oskar2517/crt-calculator/assets/2.jpg

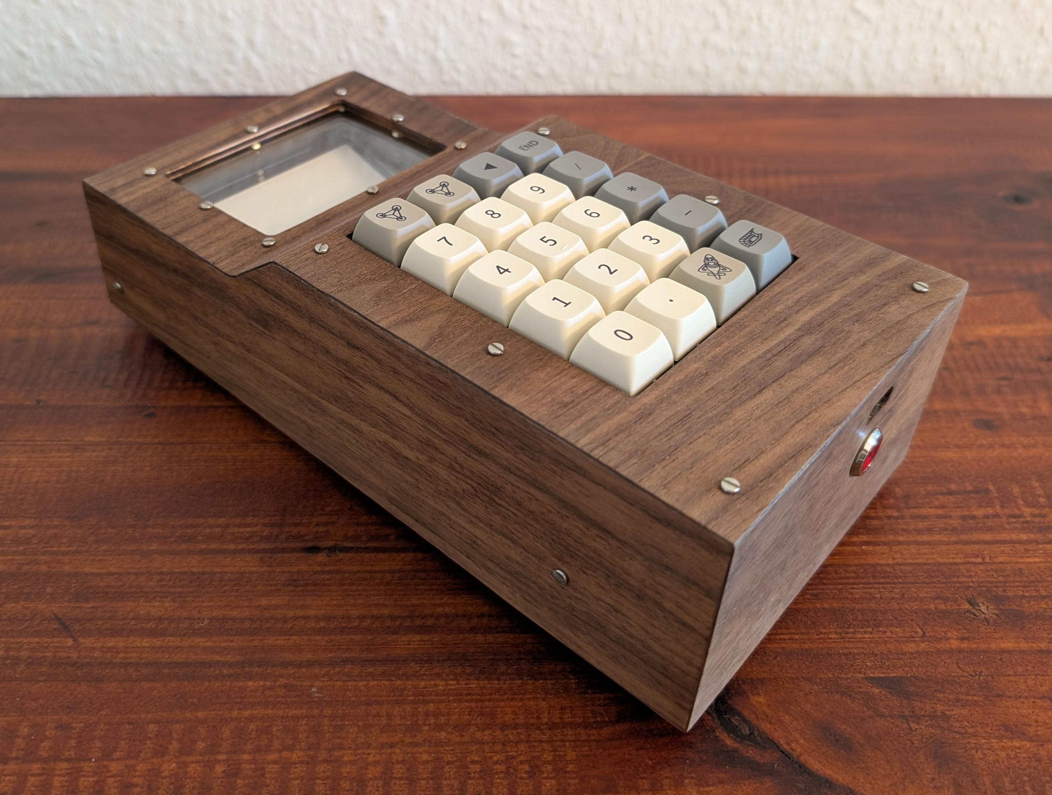
assets/2.jpg
