oskar2517/crt-calculator/assets/9.JPG

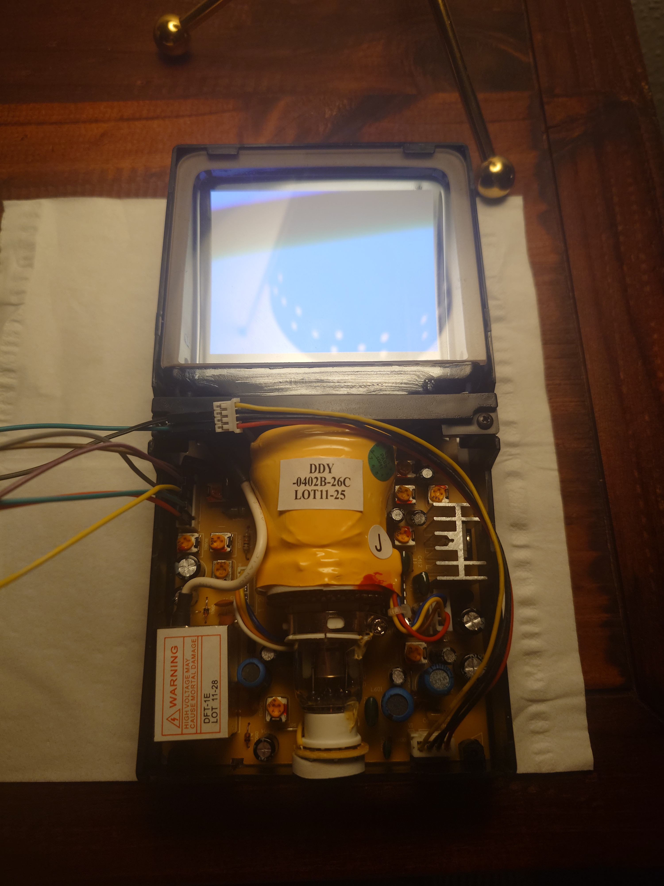
assets/9.JPG
